AndrewCromar/stepminia/graphics/blue.png

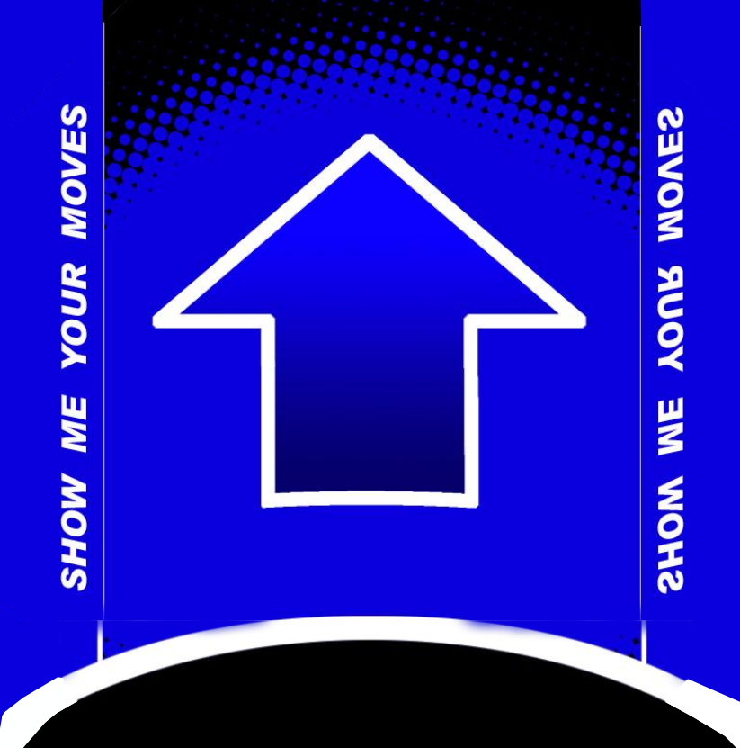
graphics/blue.png
