AndrewCromar/stepminia/graphics/pink.png

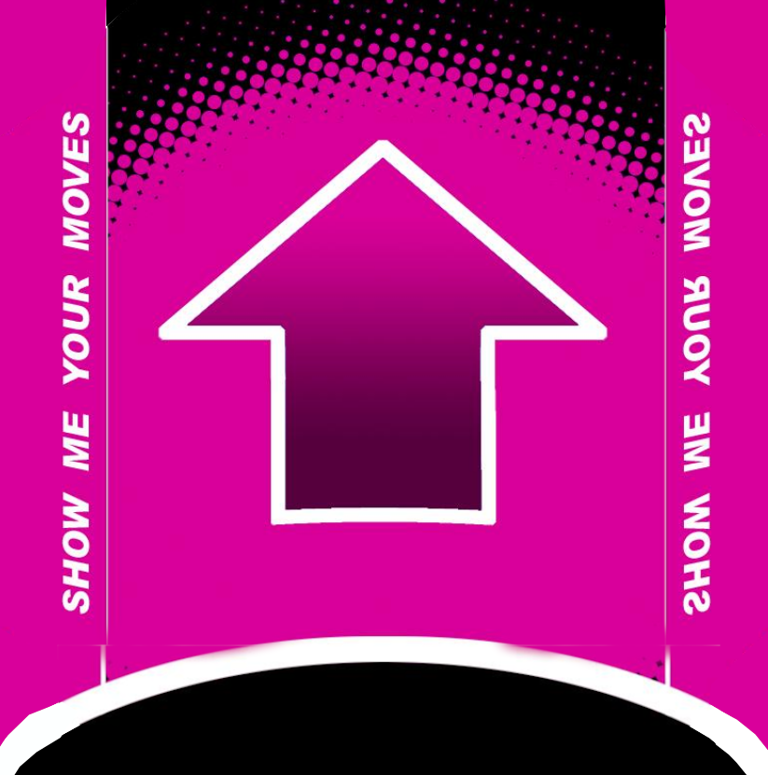
graphics/pink.png
