AndrewCromar/stepminia/website/docs/images/v1-glamor-shots/1.jpg

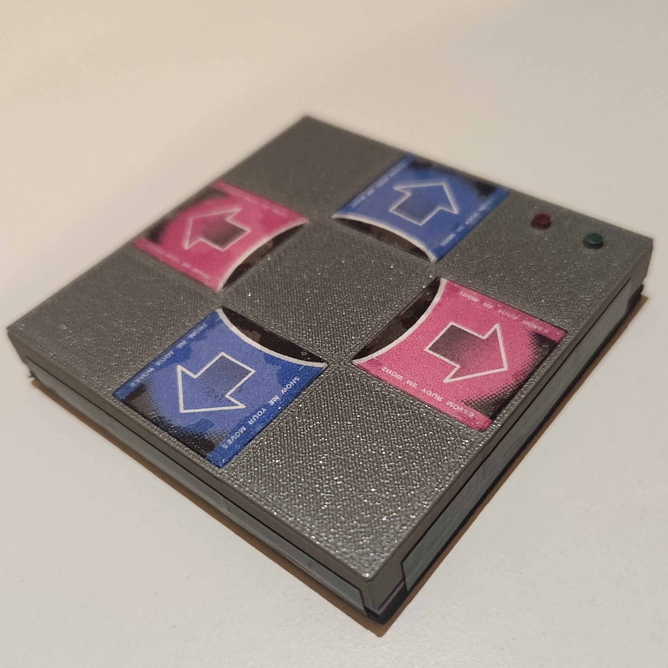
website/docs/images/v1-glamor-shots/1.jpg
