AndrewCromar/stepminia/website/docs/images/v1-glamor-shots/2.jpg

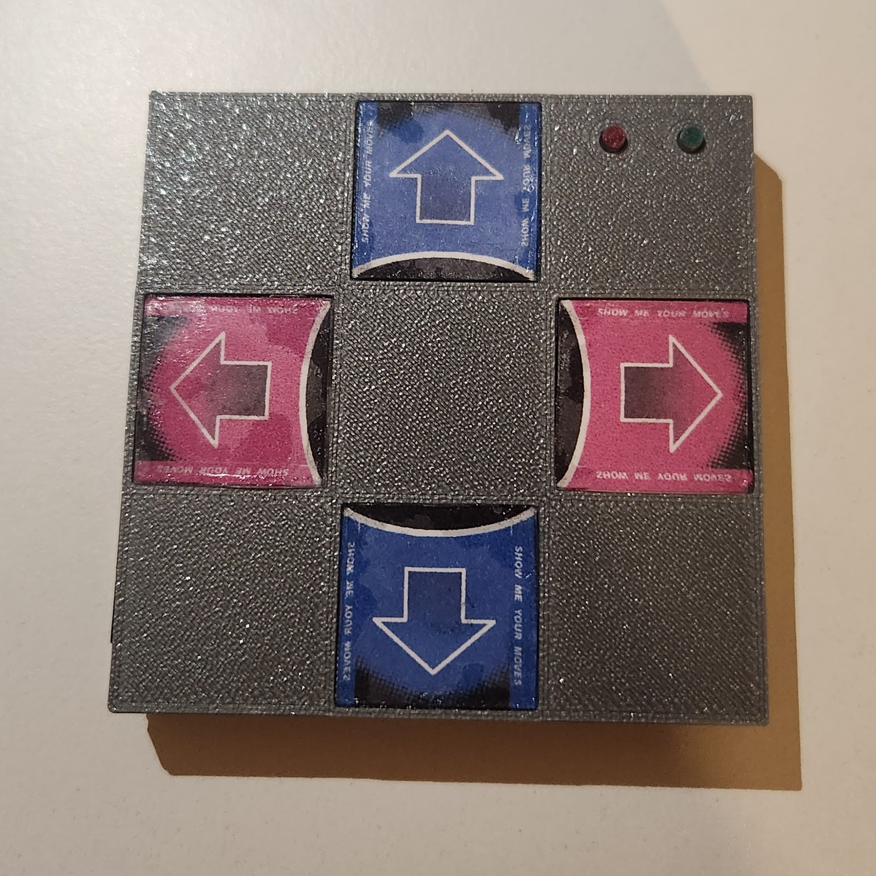
website/docs/images/v1-glamor-shots/2.jpg
