AndrewCromar/stepminia/website/docs/images/v1-glamor-shots/3.jpg

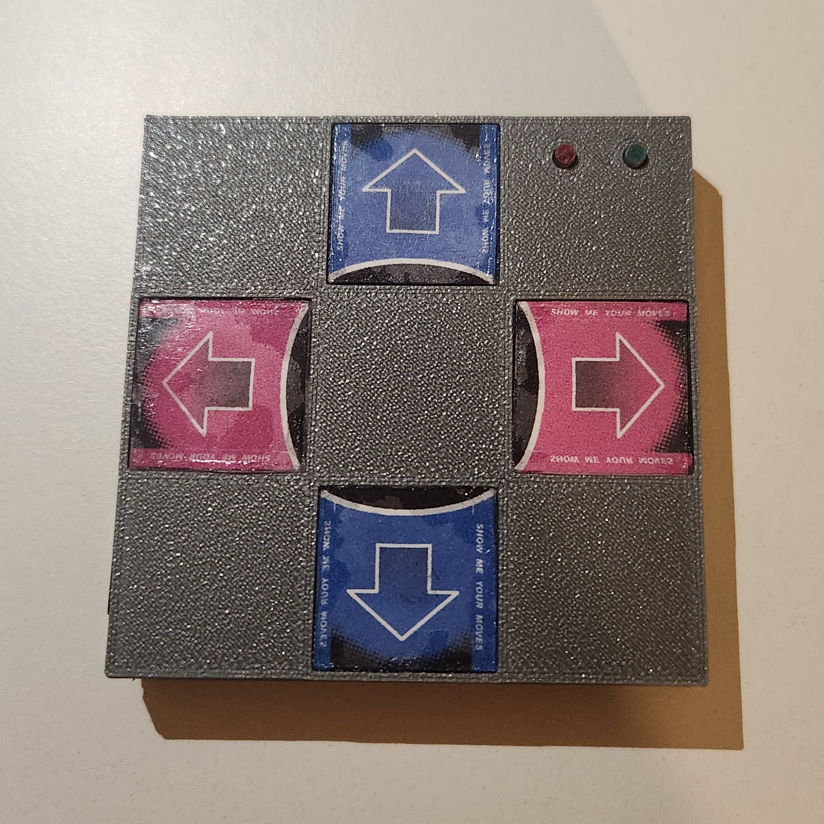
website/docs/images/v1-glamor-shots/3.jpg
