AndrewCromar/stepminia/website/docs/images/v1-glamor-shots/4.jpg

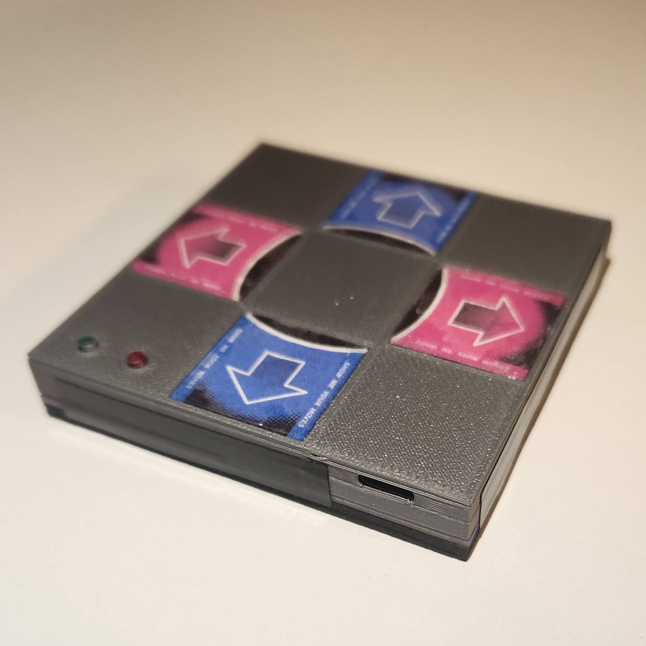
website/docs/images/v1-glamor-shots/4.jpg
