AndrewCromar/stepminia/website/docs/images/v1-glamor-shots/5.jpg

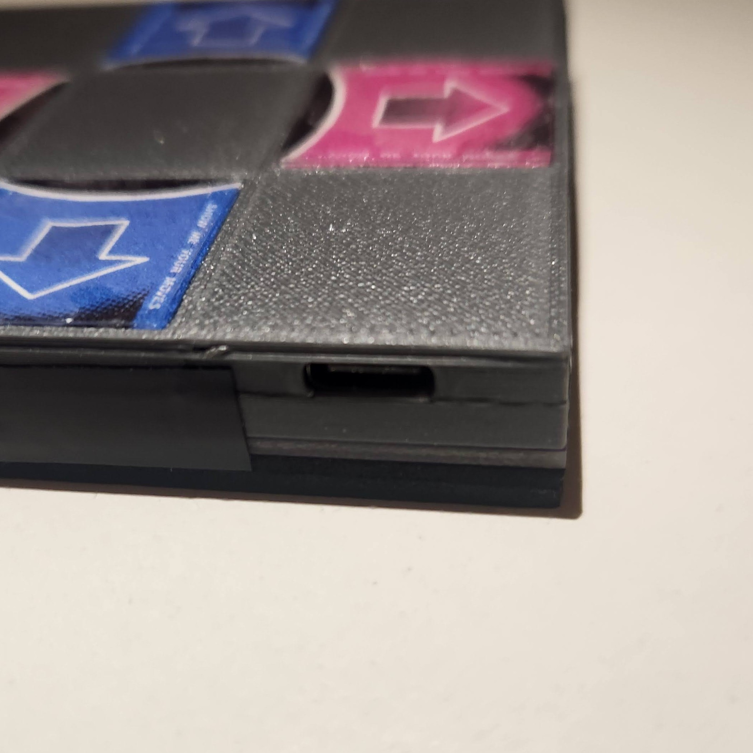
website/docs/images/v1-glamor-shots/5.jpg
