AndrewCromar/stepminia/website/docs/images/v1-glamor-shots/6.jpg

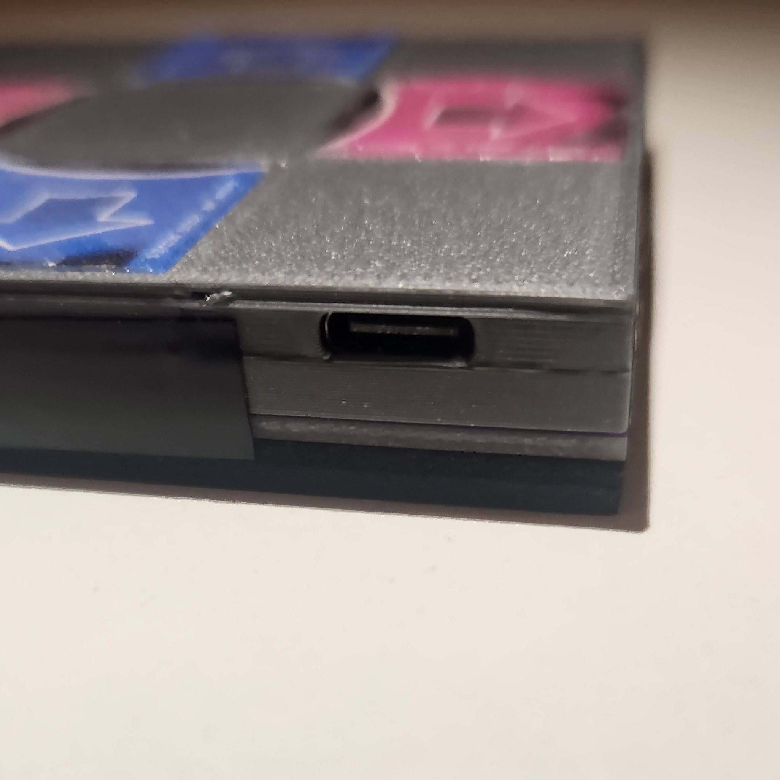
website/docs/images/v1-glamor-shots/6.jpg
