AndrewCromar/stepminia/website/docs/images/v1-glamor-shots/7.jpg

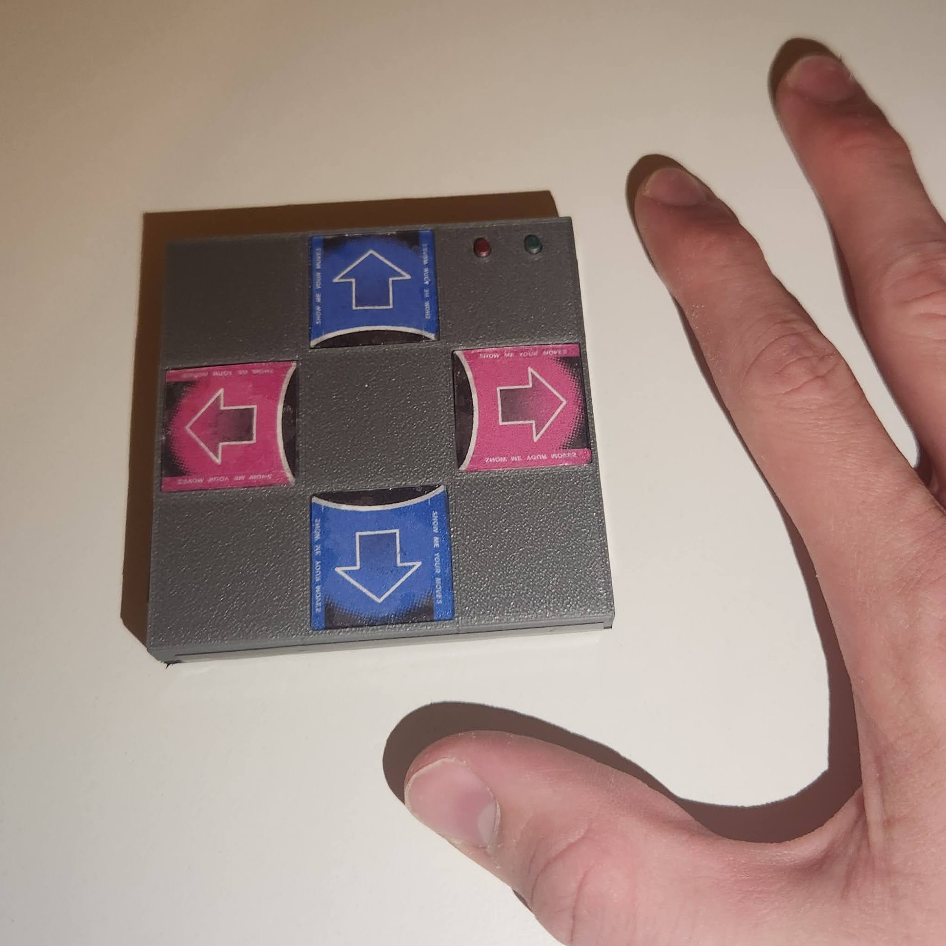
website/docs/images/v1-glamor-shots/7.jpg
