AndrewCromar/stepminia/website/docs/images/v1-glamor-shots/8.jpg

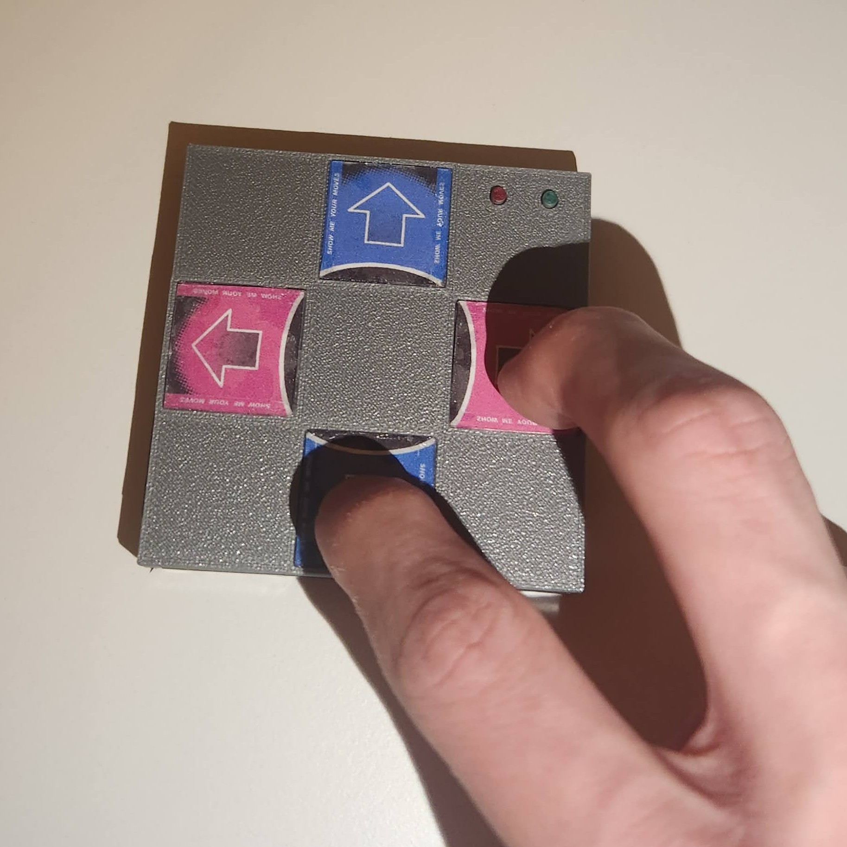
website/docs/images/v1-glamor-shots/8.jpg
