AndrewCromar/stepminia/website/docs/images/v1-glamor-shots/9.jpg

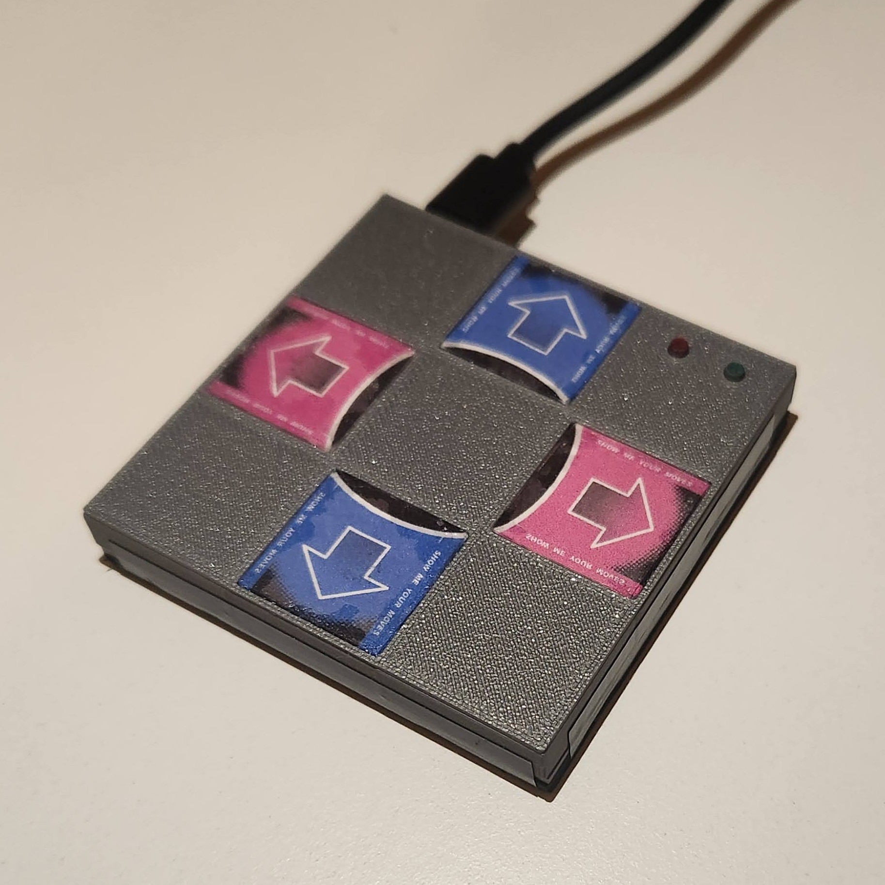
website/docs/images/v1-glamor-shots/9.jpg
