AndrewCromar/stepminia/website/docs/images/v1-glamor-shots/10.jpg

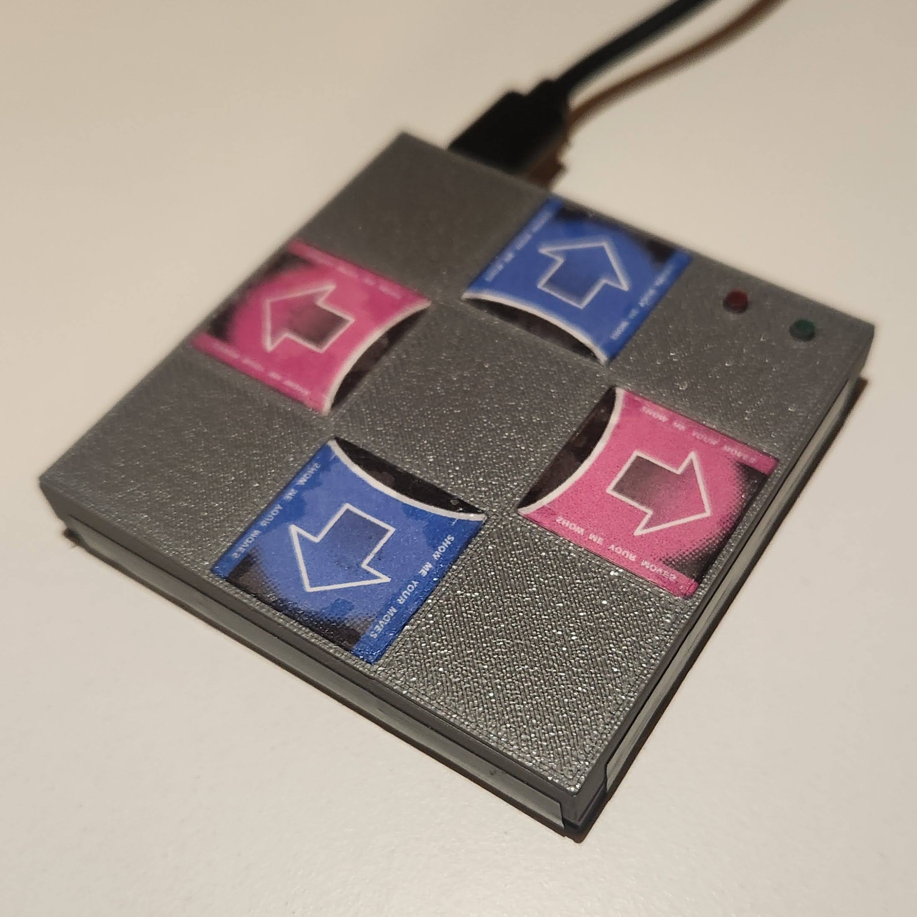
website/docs/images/v1-glamor-shots/10.jpg
