AndrewCromar/stepminia/website/docs/images/v1-glamor-shots/11.jpg

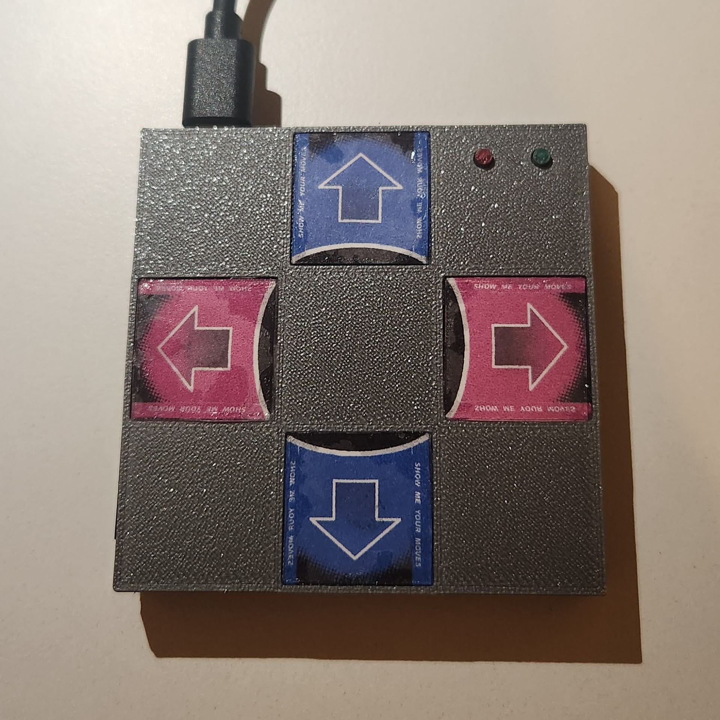
website/docs/images/v1-glamor-shots/11.jpg
